schenkzoola/PowerBrigand/docs/images/ad2.png

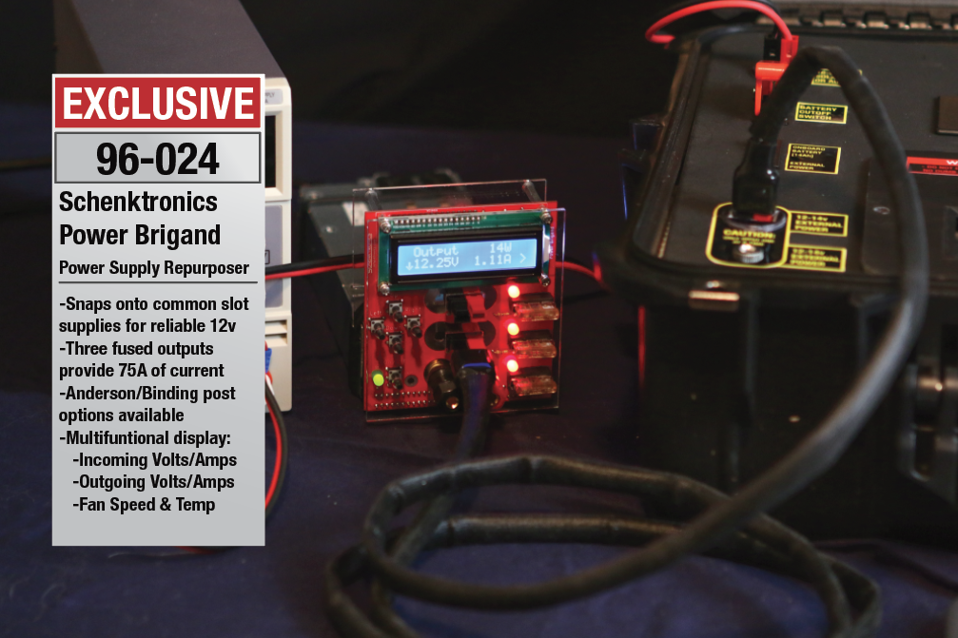
docs/images/ad2.png
