schenkzoola/PowerBrigand/docs/images/ad.jpg

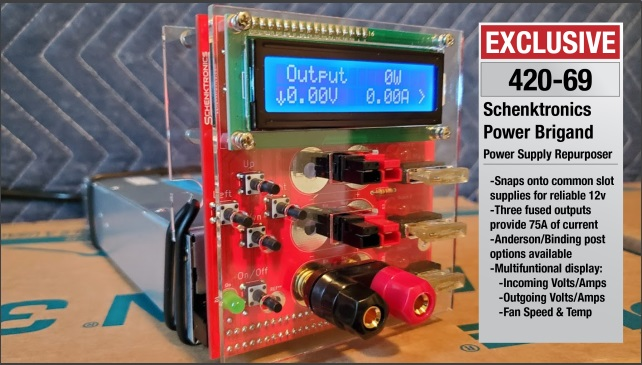
docs/images/ad.jpg
