schenkzoola/PowerBrigand/docs/images/ad_notext.jpg

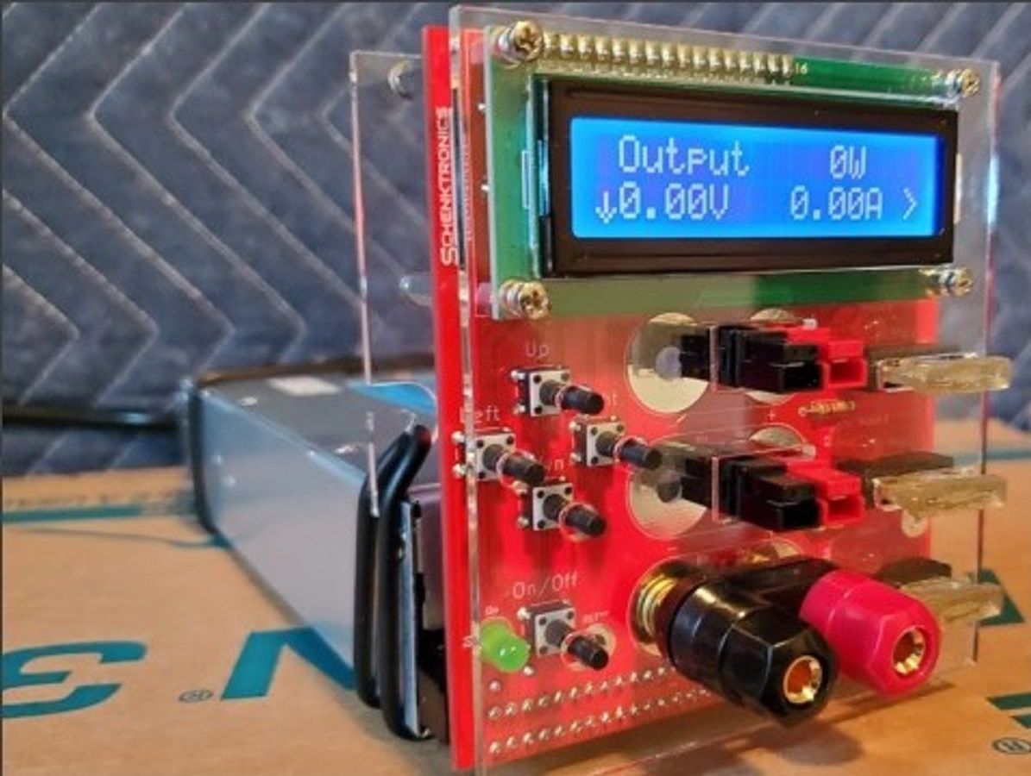
docs/images/ad_notext.jpg
