schenkzoola/PowerBrigand/docs/images/FrontNoCase.jpg

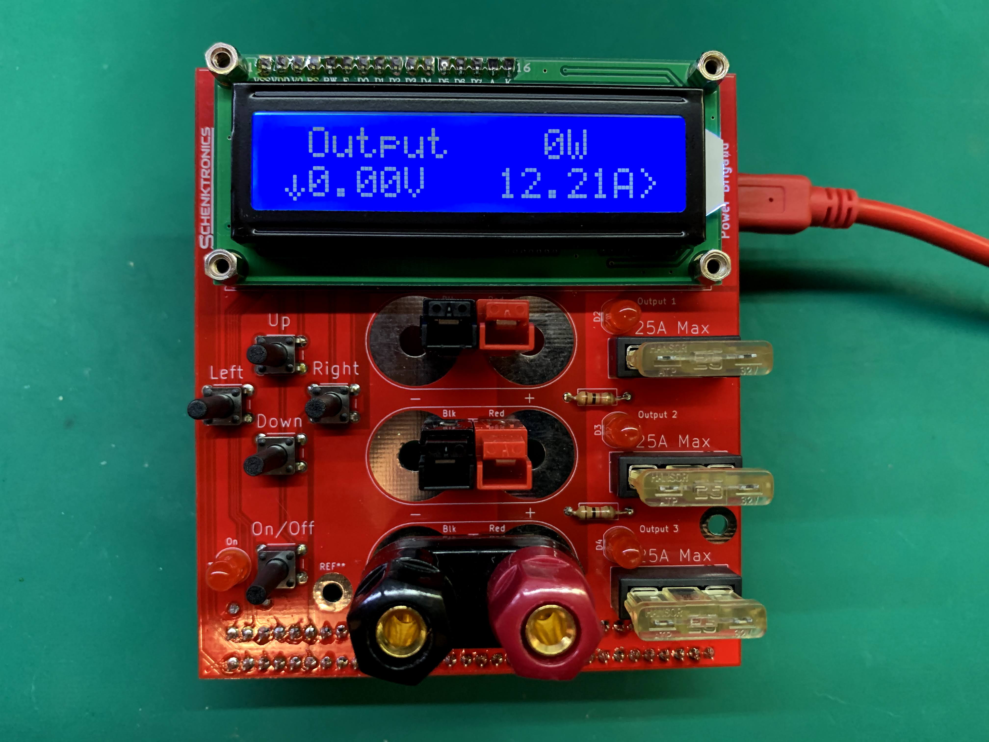
docs/images/FrontNoCase.jpg
